Yverr0y/SkySweep32/hardware/rev_c/previews/enclosure_closed.png

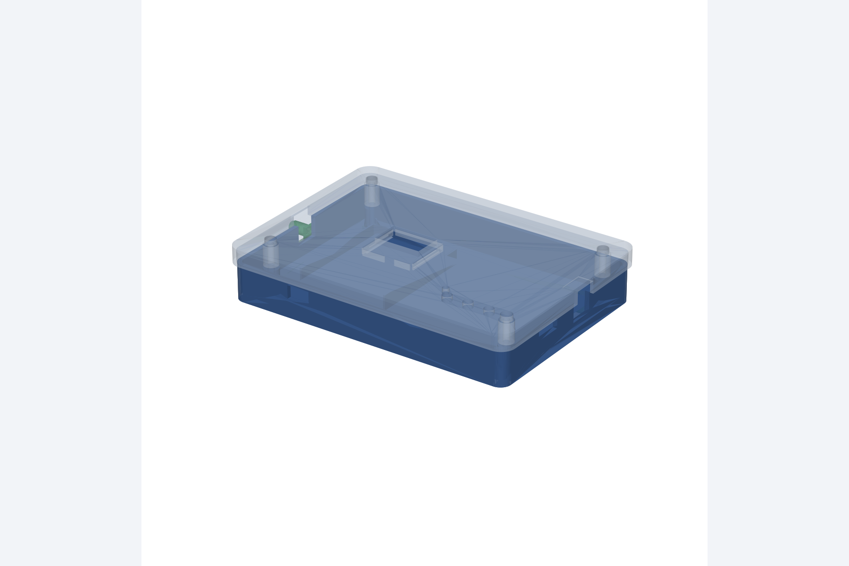
hardware/rev_c/previews/enclosure_closed.png
