Yverr0y/SkySweep32/hardware/rev_c/3dmodels/Bourns_MF_MSMF200_2_ENVELOPE.step

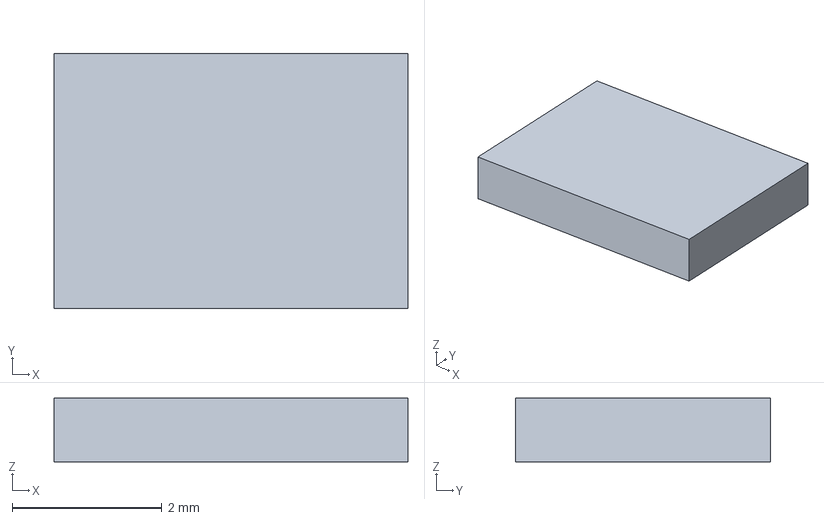
[picture p21: CAD file, 2026-08-12]
hardware/rev_c/3dmodels/Bourns_MF_MSMF200_2_ENVELOPE.step
4.73 x 3.41 x 0.85 mm
