Yverr0y/SkySweep32/hardware/rev_c/enclosure/skysweep32_rev_c_cutaway.step

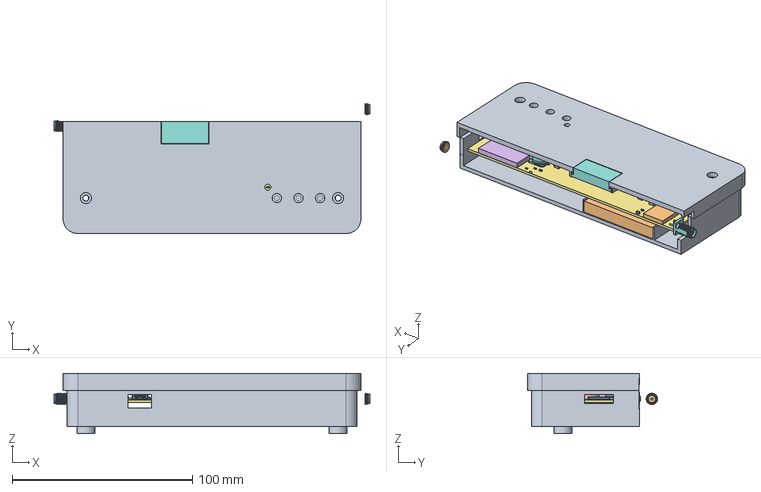
[picture p22: CAD file, 2026-08-12]
hardware/rev_c/enclosure/skysweep32_rev_c_cutaway.step
175.4 x 72.2 x 33.5 mm
