Yverr0y/SkySweep32/hardware/rev_c/3dmodels/ADI_MAX17048_TDFN8_ENVELOPE.step

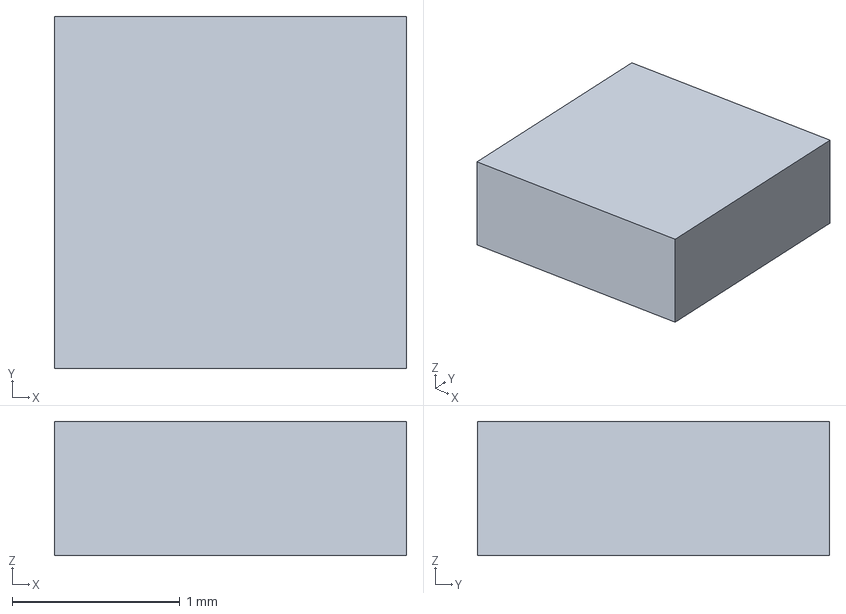
[picture p23: CAD file, 2026-08-12]
hardware/rev_c/3dmodels/ADI_MAX17048_TDFN8_ENVELOPE.step
2.10 x 2.10 x 0.8 mm
