Yverr0y/SkySweep32/hardware/rev_c/3dmodels/UBlox_SAM_M10Q_ENVELOPE.step

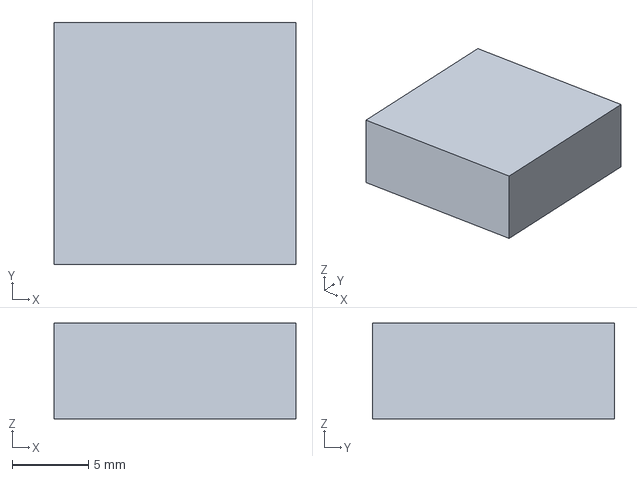
[picture p24: CAD file, 2026-08-12]
hardware/rev_c/3dmodels/UBlox_SAM_M10Q_ENVELOPE.step
15.9 x 15.9 x 6.30 mm
