Yverr0y/SkySweep32/hardware/rev_c/3dmodels/Molex_104031_0811_WITH_CARD_ENVELOPE.step

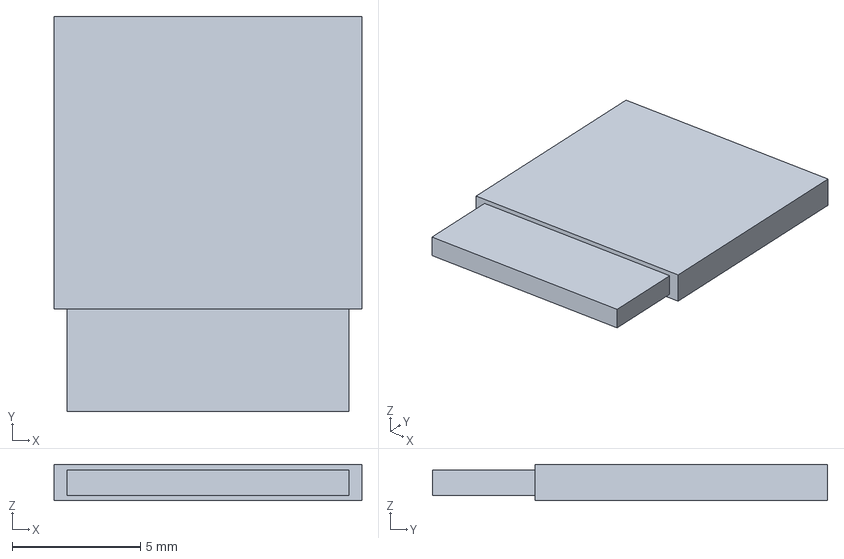
[picture p25: CAD file, 2026-08-12]
hardware/rev_c/3dmodels/Molex_104031_0811_WITH_CARD_ENVELOPE.step
12.0 x 15.4 x 1.42 mm
