Yverr0y/SkySweep32/hardware/rev_c/3dmodels/TI_BQ24074_RGT_ENVELOPE.step

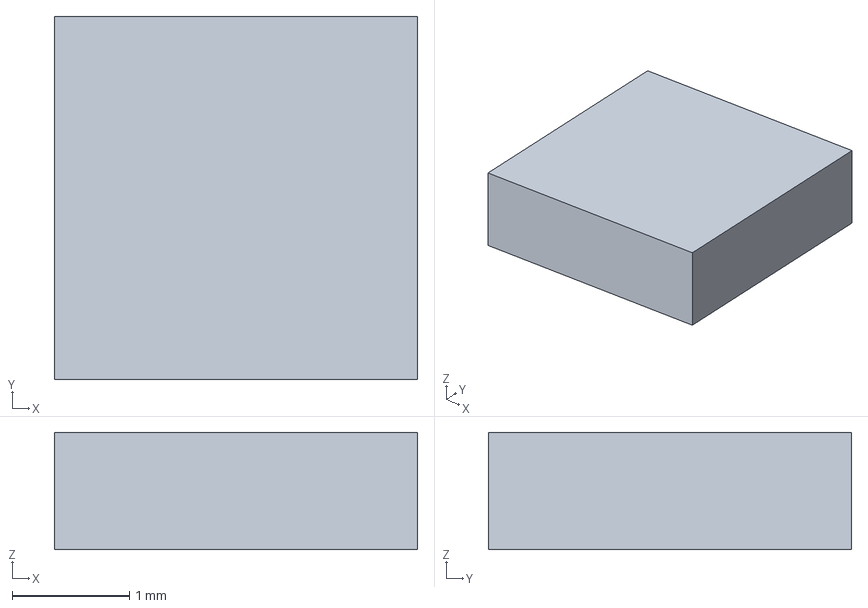
[picture p26: CAD file, 2026-08-12]
hardware/rev_c/3dmodels/TI_BQ24074_RGT_ENVELOPE.step
3.10 x 3.10 x 1.00 mm
