Yverr0y/SkySweep32/hardware/rev_c/3dmodels/Adafruit_OLED_PID326_ENVELOPE.step

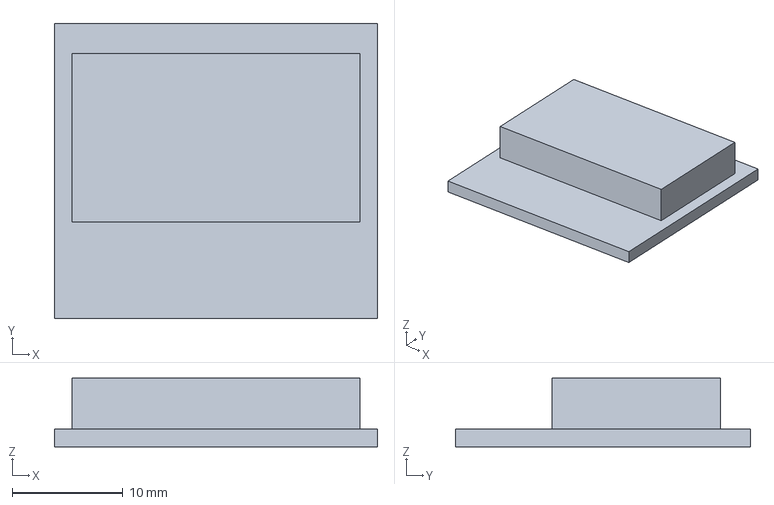
[picture p27: CAD file, 2026-08-12]
hardware/rev_c/3dmodels/Adafruit_OLED_PID326_ENVELOPE.step
29.2 x 26.7 x 6.20 mm
