Yverr0y/SkySweep32/hardware/rev_c/3dmodels/RX5808_2012_12P_ENVELOPE.step

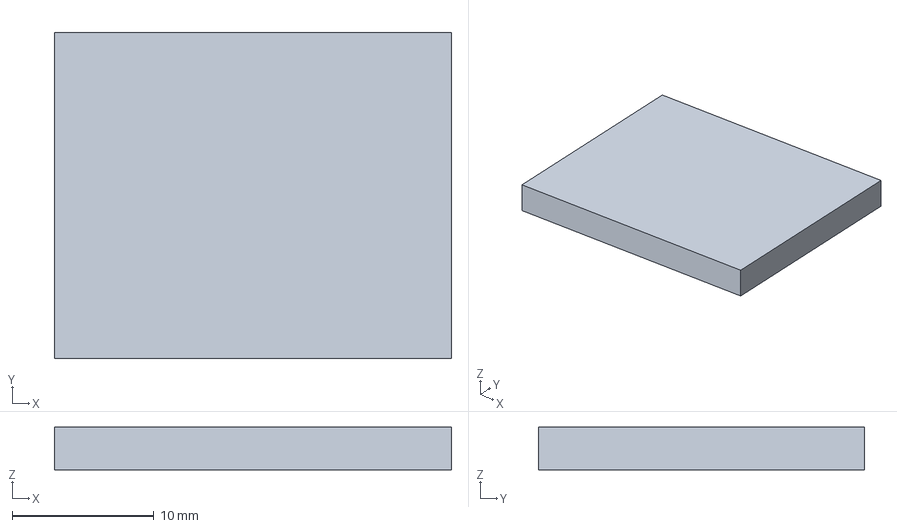
[picture p28: CAD file, 2026-08-12]
hardware/rev_c/3dmodels/RX5808_2012_12P_ENVELOPE.step
28.0 x 23.0 x 3.00 mm
